croissantking/G3-Personality-Card-USB/Whisper/Whisper Card USB V2.kicad_sch

## KiCad design Whisper/Whisper Card USB V2.kicad_sch (2023-07-12)

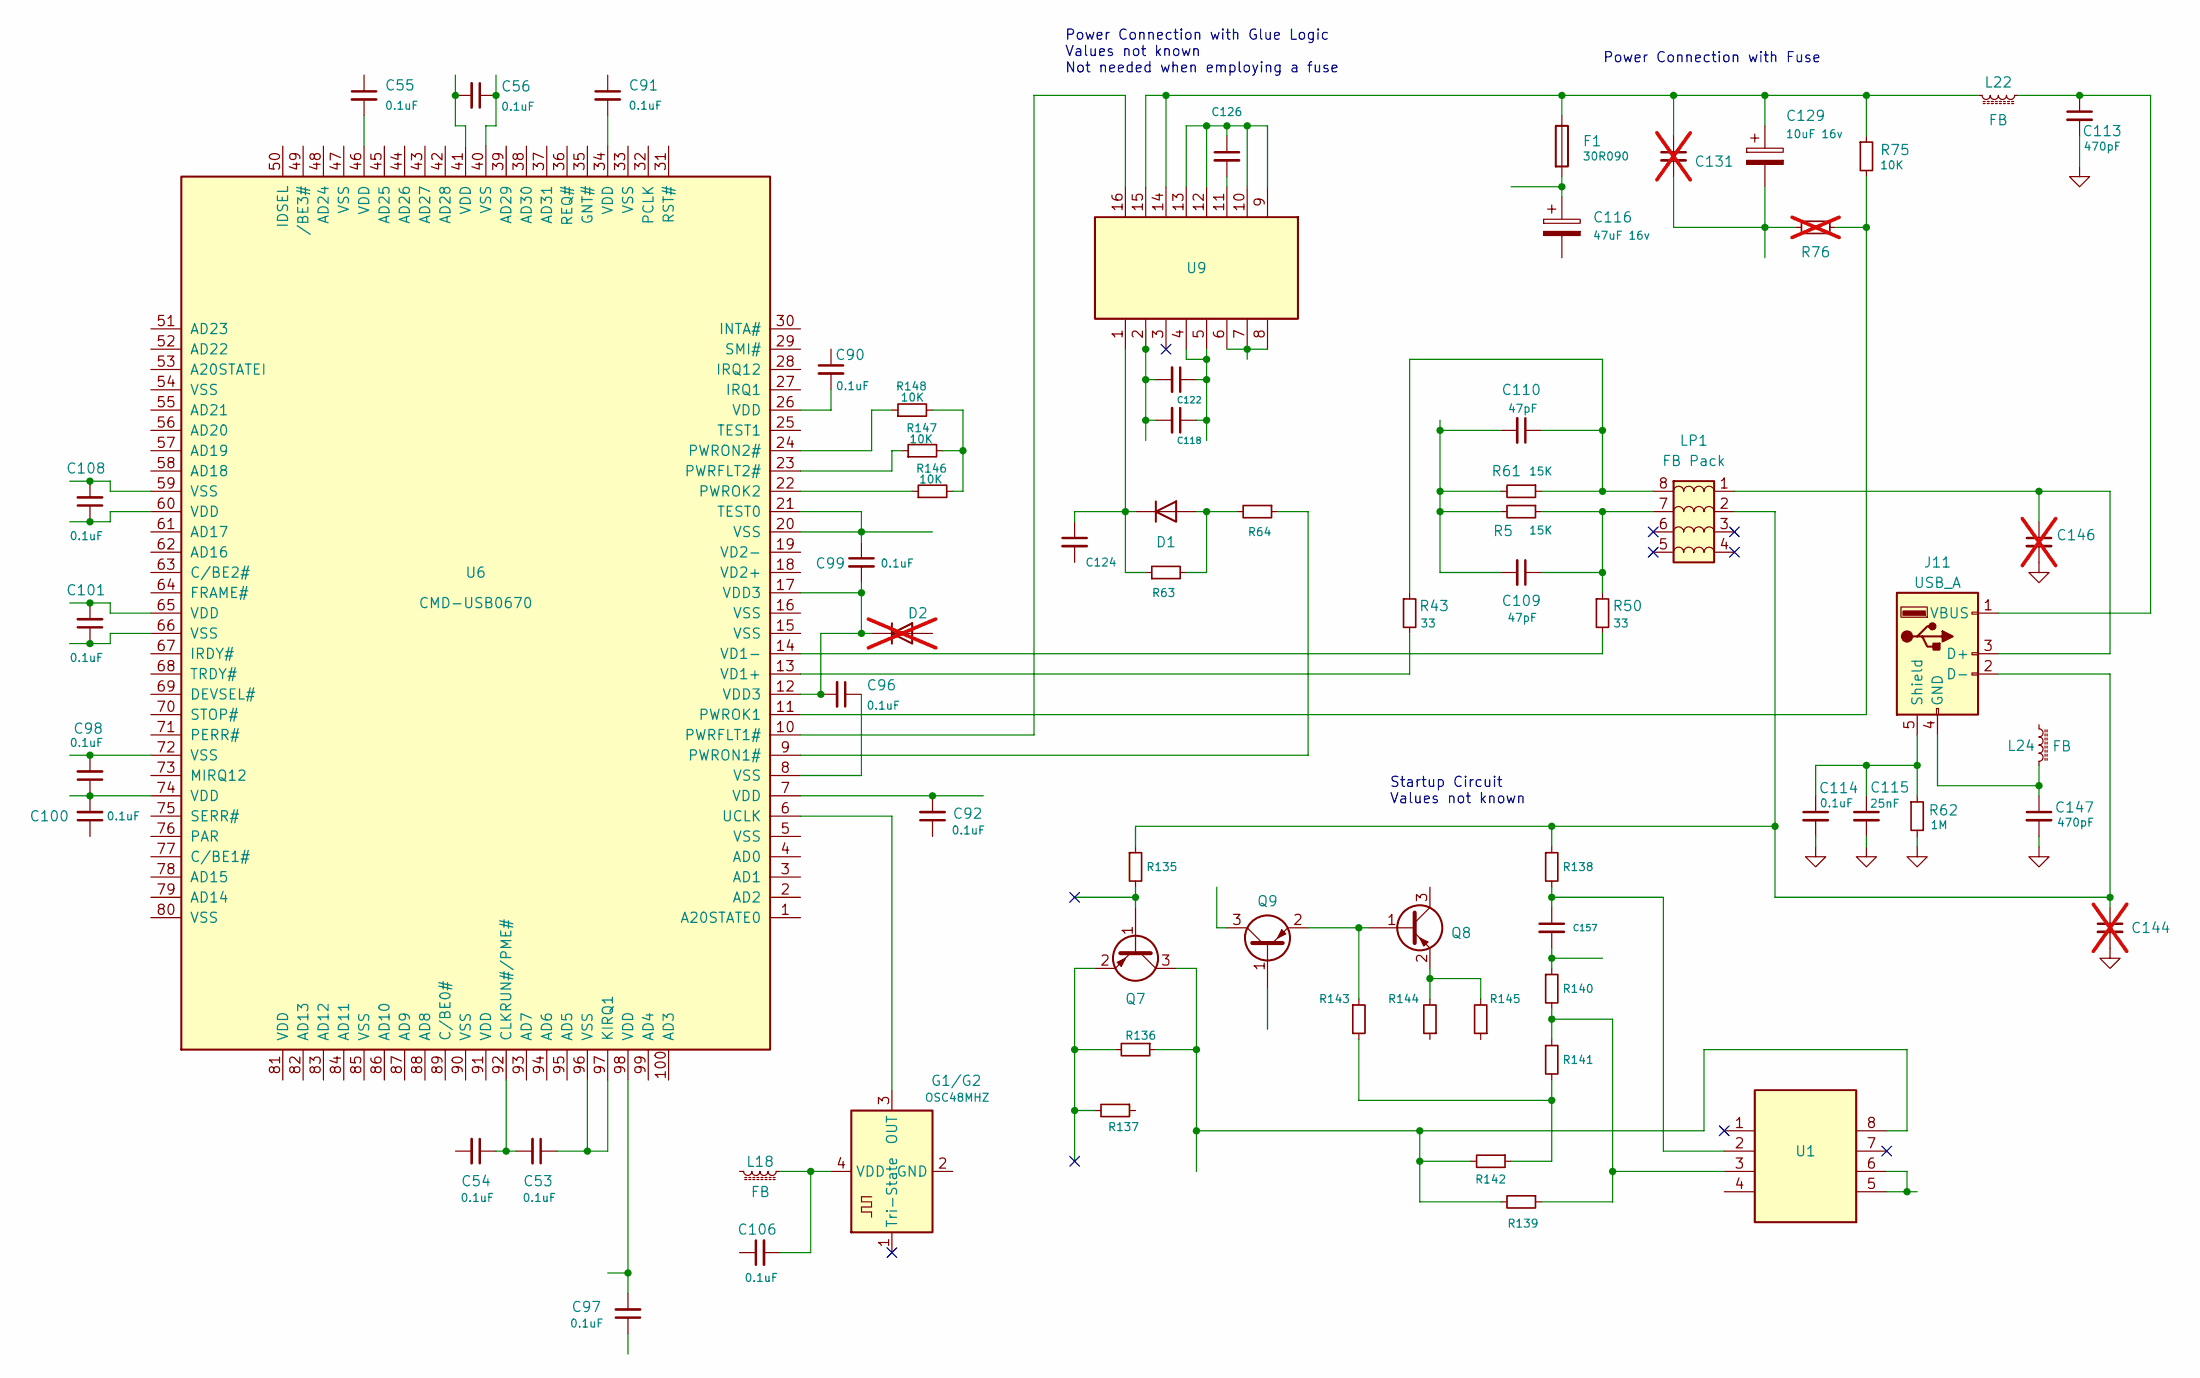
[picture p8: schematic Whisper Card USB V2.kicad_sch]

Parts:
C53, C54, C55, C56, C90, C91, C92, C96, C97, C98, C99, C100, C101, C106, C108, C114: 0.1uF
C109, C110: 47pF
C113, C147: 470pF
C115: 25nF
C116: 47uF 16v
C118, C122, C124, C126, C157: C_Small
C129: 10uF 16v
C131: 1.1nf; not fitted
C144, C146: ???; not fitted
D1: D
D2: D; not fitted
F1: 30R090
G1/G2: OSC48MHZ; Oscillator_SMD_Abracon_ASCO-4Pin_1.6x1.2mm
J11: USB_A
L18, L22, L24: FB
LP1: FB Pack
Q7, Q8, Q9: MMBT3906; SOT-23
R5, R61: 15K
R43, R50: 33
R62: 1M
R63, R64, R135, R136, R137, R138, R139, R140, R141, R142, R143, R144, R145: R_Small
R75, R146, R147, R148: 10K
R76: not fitted
U1, U9: LTC1865-S8; SOIC-8_3.9x4.9mm_P1.27mm
U6: CMD-USB0670; LQFP-100_14x14mm_P0.5mm

Connections:
GND: C113.2, C114.2, C115.2, C144.2, C146.2, C147.2, R62.2
unnamed: C53.1, U6.96 (VSS), U6.97 (KIRQ1)
unnamed: C53.2, C54.1, U6.92 (CLKRUN#/PME#)
unnamed: C55.2, U6.46 (VDD)
unnamed: C56.1, U6.40 (VSS)
unnamed: C56.2, U6.41 (VDD)
unnamed: C90.2, U6.26 (VDD)
unnamed: C91.2, U6.34 (VDD)
unnamed: C92.2, U6.7 (VDD)
unnamed: C96.1, U6.8 (VSS)
unnamed: C96.2, C99.2, D2.1 (K), U6.12 (VDD3), U6.17 (VDD3)
unnamed: C97.2, U6.98 (VDD)
unnamed: C98.2, U6.72 (VSS)
unnamed: C99.1, U6.20 (VSS), U6.21 (TEST0)
unnamed: C98.1, C100.2, U6.74 (VDD)
unnamed: C101.1, U6.66 (VSS)
unnamed: C101.2, U6.65 (VDD)
unnamed: C106.2, G1/G2.4 (VDD), L18.1
unnamed: C108.1, U6.60 (VDD)
unnamed: C108.2, U6.59 (VSS)
unnamed: C109.1, LP1.7, R5.1, R50.1
unnamed: C109.2, C110.2, R5.2, R61.2
unnamed: C110.1, LP1.8, R43.1, R61.1
unnamed: C113.1, J11.1 (VBUS), L22.1
unnamed: C114.1, C115.1, J11.5 (Shield), R62.1
unnamed: C116.1, F1.2
unnamed: C118.1, C122.1, U9.4, U9.5
unnamed: C118.2, C122.2, U9.2
unnamed: C124.1, D1.1 (K), R63.1, U9.1
unnamed: C126.1, U9.9, U9.10, U9.12, U9.13
unnamed: C126.2, U9.11
unnamed: C129.1, C131.1, F1.1, L22.2, R75.1, U9.14, U9.15
unnamed: C129.2, C131.2, R76.2
unnamed: C144.1, J11.2 (D-), LP1.2, R135.1, R138.1
unnamed: C146.1, J11.3 (D+), LP1.1
unnamed: C147.1, J11.4 (GND), L24.2
unnamed: C157.1, R138.2, U1.2
unnamed: C157.2, R140.1
unnamed: D1.2 (A), R63.2, R64.2
unnamed: G1/G2.3 (OUT), U6.6 (UCLK)
unnamed: Q7.1 (B), R135.2
unnamed: Q7.2 (E), R136.2, R137.2
unnamed: Q7.3 (C), R136.1, R139.2, R142.2, U1.8
unnamed: Q8.1 (B), Q9.2 (E), R143.1
unnamed: Q8.2 (E), R144.2, R145.2
unnamed: R43.2, U6.13 (VD1+)
unnamed: R50.2, U6.14 (VD1-)
unnamed: R64.1, U6.9 (PWRON1#)
unnamed: R75.2, R76.1, U6.11 (PWROK1)
unnamed: R139.1, R140.2, R141.1, U1.3
unnamed: R141.2, R142.1, R143.2
unnamed: R146.1, U6.22 (PWROK2)
unnamed: R146.2, R147.2, R148.2
unnamed: R147.1, U6.23 (PWRFLT2#)
unnamed: R148.1, U6.24 (PWRON2#)
unnamed: U1.5, U1.6
unnamed: U6.10 (PWRFLT1#), U9.16
unnamed: U9.6, U9.7, U9.8

Notes on the sheet:
Startup Circuit Values not known
Power Connection with Glue Logic Values not known Not needed when employing a fuse
Power Connection with Fuse
