croissantking/G3-Personality-Card-USB/Whisper/Whisper USB V5.kicad_sch

## KiCad design Whisper/Whisper USB V5.kicad_sch (2025-03-09)

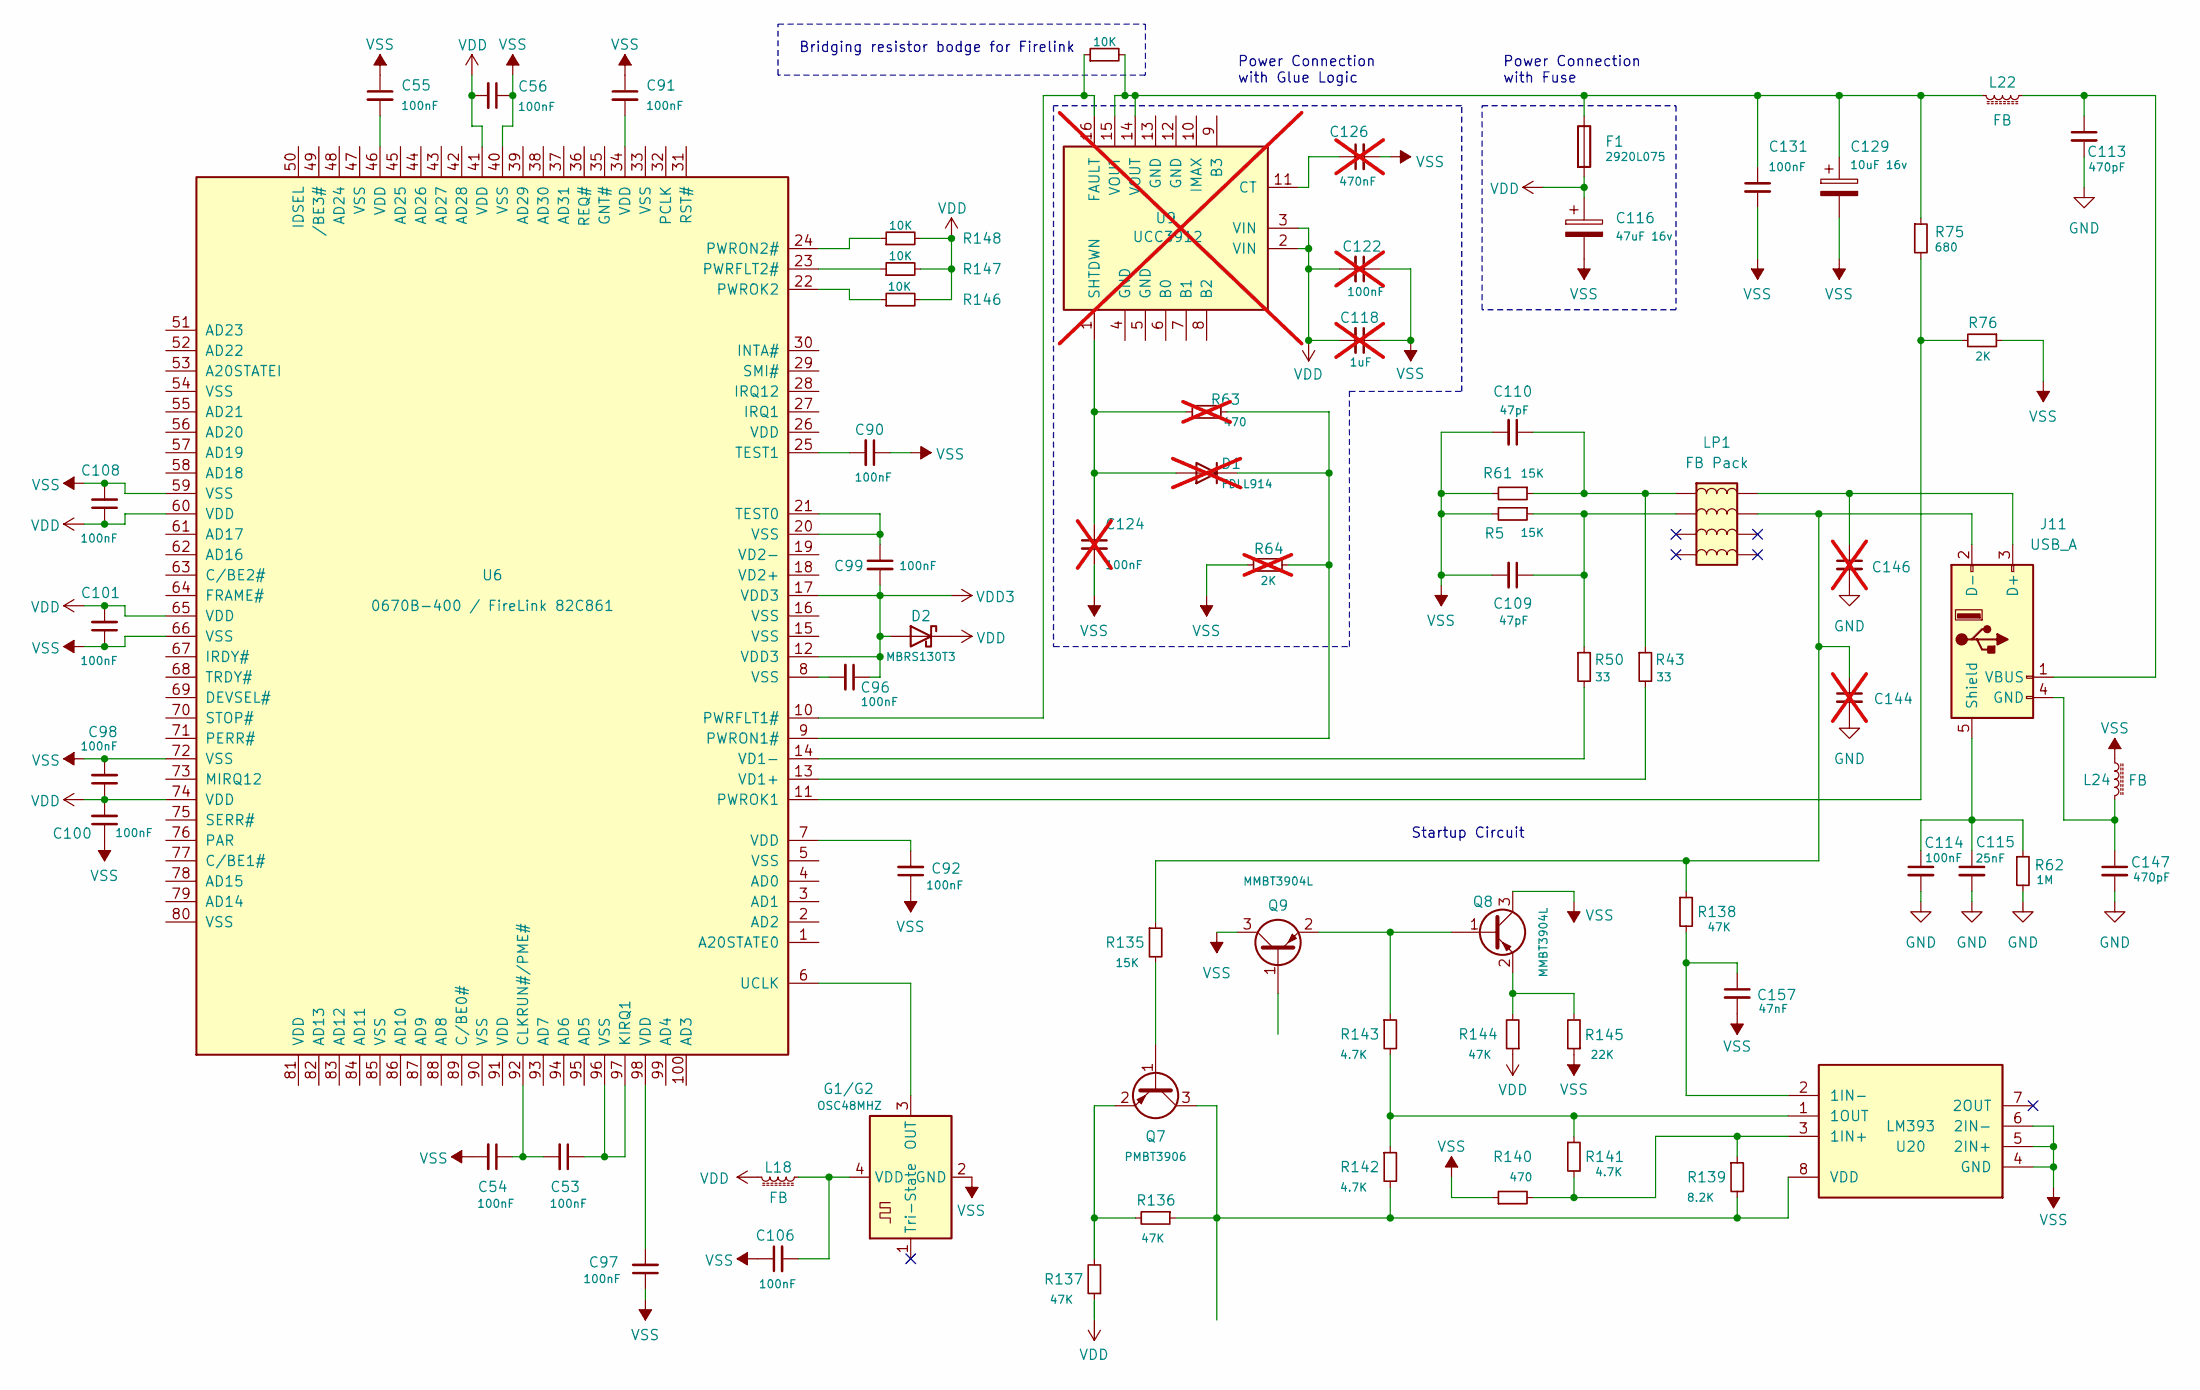
[picture p9: schematic Whisper USB V5.kicad_sch]

Parts:
C53, C54, C55, C56, C90, C91, C92, C96, C97, C98, C99, C100, C101, C106, C108, C114, C131: 100nF
C109, C110: 47pF
C113, C147: 470pF
C115: 25nF
C116: 47uF 16v
C118: 1uF; not fitted
C122, C124: 100nF; not fitted
C126: 470nF; not fitted
C129: 10uF 16v
C144, C146: ???; not fitted
C157: 47nF
D1: FDLL914; not fitted
D2: MBRS130T3
F1: 2920L075
G1/G2: OSC48MHZ; Oscillator_SMD_Abracon_ASCO-4Pin_1.6x1.2mm
J11: USB_A
L18, L22, L24: FB
LP1: FB Pack
Q7: PMBT3906; SOT-23
Q8, Q9: MMBT3904L; SOT-23
R1, R146, R147, R148: 10K
R5, R61, R135: 15K
R43, R50: 33
R62: 1M
R63: 470; not fitted
R64: 2K; not fitted
R75: 680
R76: 2K
R136, R137, R138, R144: 47K
R139: 8.2K
R140: 470
R141, R142, R143: 4.7K
R145: 22K
U6: 0670B-400 / FireLink 82C861; LQFP-100_14x14mm_P0.5mm
U9: UCC3912; SOIC-8_3.9x4.9mm_P1.27mm; not fitted
U20: LM393; SOIC-8_3.9x4.9mm_P1.27mm

Connections:
GND: C113.2, C114.2, C115.2, C144.2, C146.2, C147.2, R62.2
unnamed: C53.1, U6.96 (VSS), U6.97 (KIRQ1)
unnamed: C53.2, C54.1, U6.92 (CLKRUN#/PME#)
unnamed: C55.2, U6.46 (VDD)
unnamed: C90.2, U6.25 (TEST1)
unnamed: C91.2, U6.34 (VDD)
unnamed: C92.2, U6.7 (VDD)
unnamed: C96.2, U6.8 (VSS)
unnamed: C97.2, U6.98 (VDD)
unnamed: C99.1, U6.20 (VSS), U6.21 (TEST0)
unnamed: C106.2, G1/G2.4 (VDD), L18.1
unnamed: C109.1, LP1.7, R5.1, R50.1
unnamed: C110.1, LP1.8, R43.1, R61.1
unnamed: C113.1, J11.1 (VBUS), L22.1
unnamed: C114.1, C115.1, J11.5 (Shield), R62.1
unnamed: C124.1, D1.2 (A), R63.1, U9.1 (SHTDWN)
unnamed: C126.1, U9.11 (CT)
unnamed: C129.1, C131.1, F1.1, L22.2, R1.2, R75.1, U9.14 (VOUT), U9.15 (VOUT)
unnamed: C144.1, J11.2 (D-), LP1.2, R135.1, R138.1
unnamed: C146.1, J11.3 (D+), LP1.1
unnamed: C147.1, J11.4 (GND), L24.2
unnamed: C157.1, R138.2, U20.2 (1IN-)
unnamed: D1.1 (K), R63.2, R64.1, U6.9 (PWRON1#)
unnamed: G1/G2.3 (OUT), U6.6 (UCLK)
unnamed: Q7.1 (B), R135.2
unnamed: Q7.2 (E), R136.2, R137.2
unnamed: Q7.3 (C), R136.1, R139.2, R142.2, U20.8 (VDD)
unnamed: Q8.1 (B), Q9.2 (E), R143.1
unnamed: Q8.2 (E), R144.2, R145.2
unnamed: R1.1, U6.10 (PWRFLT1#), U9.16 (FAULT)
unnamed: R43.2, U6.13 (VD1+)
unnamed: R50.2, U6.14 (VD1-)
unnamed: R75.2, R76.2, U6.11 (PWROK1)
unnamed: R139.1, R140.2, R141.2, U20.3 (1IN+)
unnamed: R141.1, R142.1, R143.2, U20.1 (1OUT)
unnamed: R146.1, U6.22 (PWROK2)
unnamed: R147.1, U6.23 (PWRFLT2#)
unnamed: R148.1, U6.24 (PWRON2#)
VDD: C56.2, C98.1, C100.2, C101.2, C108.1, C116.1, C118.2, C122.2, D2.1 (K), F1.2, L18.2, R137.1, R144.1, R146.2, R147.2, R148.2, U6.41 (VDD), U6.60 (VDD), U6.65 (VDD), U6.74 (VDD), U9.2 (VIN), U9.3 (VIN)
VDD3: C96.1, C99.2, D2.2 (A), U6.12 (VDD3), U6.17 (VDD3)
VSS: C54.2, C55.1, C56.1, C90.1, C91.1, C92.1, C97.1, C98.2, C100.1, C101.1, C106.1, C108.2, C109.2, C110.2, C116.2, C118.1, C122.1, C124.2, C126.2, C129.2, C131.2, C157.2, G1/G2.2 (GND), L24.1, Q8.3 (C), Q9.3 (C), R5.2, R61.2, R64.2, R76.1, R140.1, R145.1, U6.40 (VSS), U6.59 (VSS), U6.66 (VSS), U6.72 (VSS), U20.4 (GND), U20.5 (2IN+), U20.6 (2IN-)

Notes on the sheet:
Startup Circuit
Power Connection with Glue Logic
Power Connection with Fuse
Bridging resistor bodge for Firelink
