croissantking/G3-Personality-Card-USB/Wings/Wings USB V3.kicad_sch

## KiCad design Wings/Wings USB V3.kicad_sch (2025-03-09)

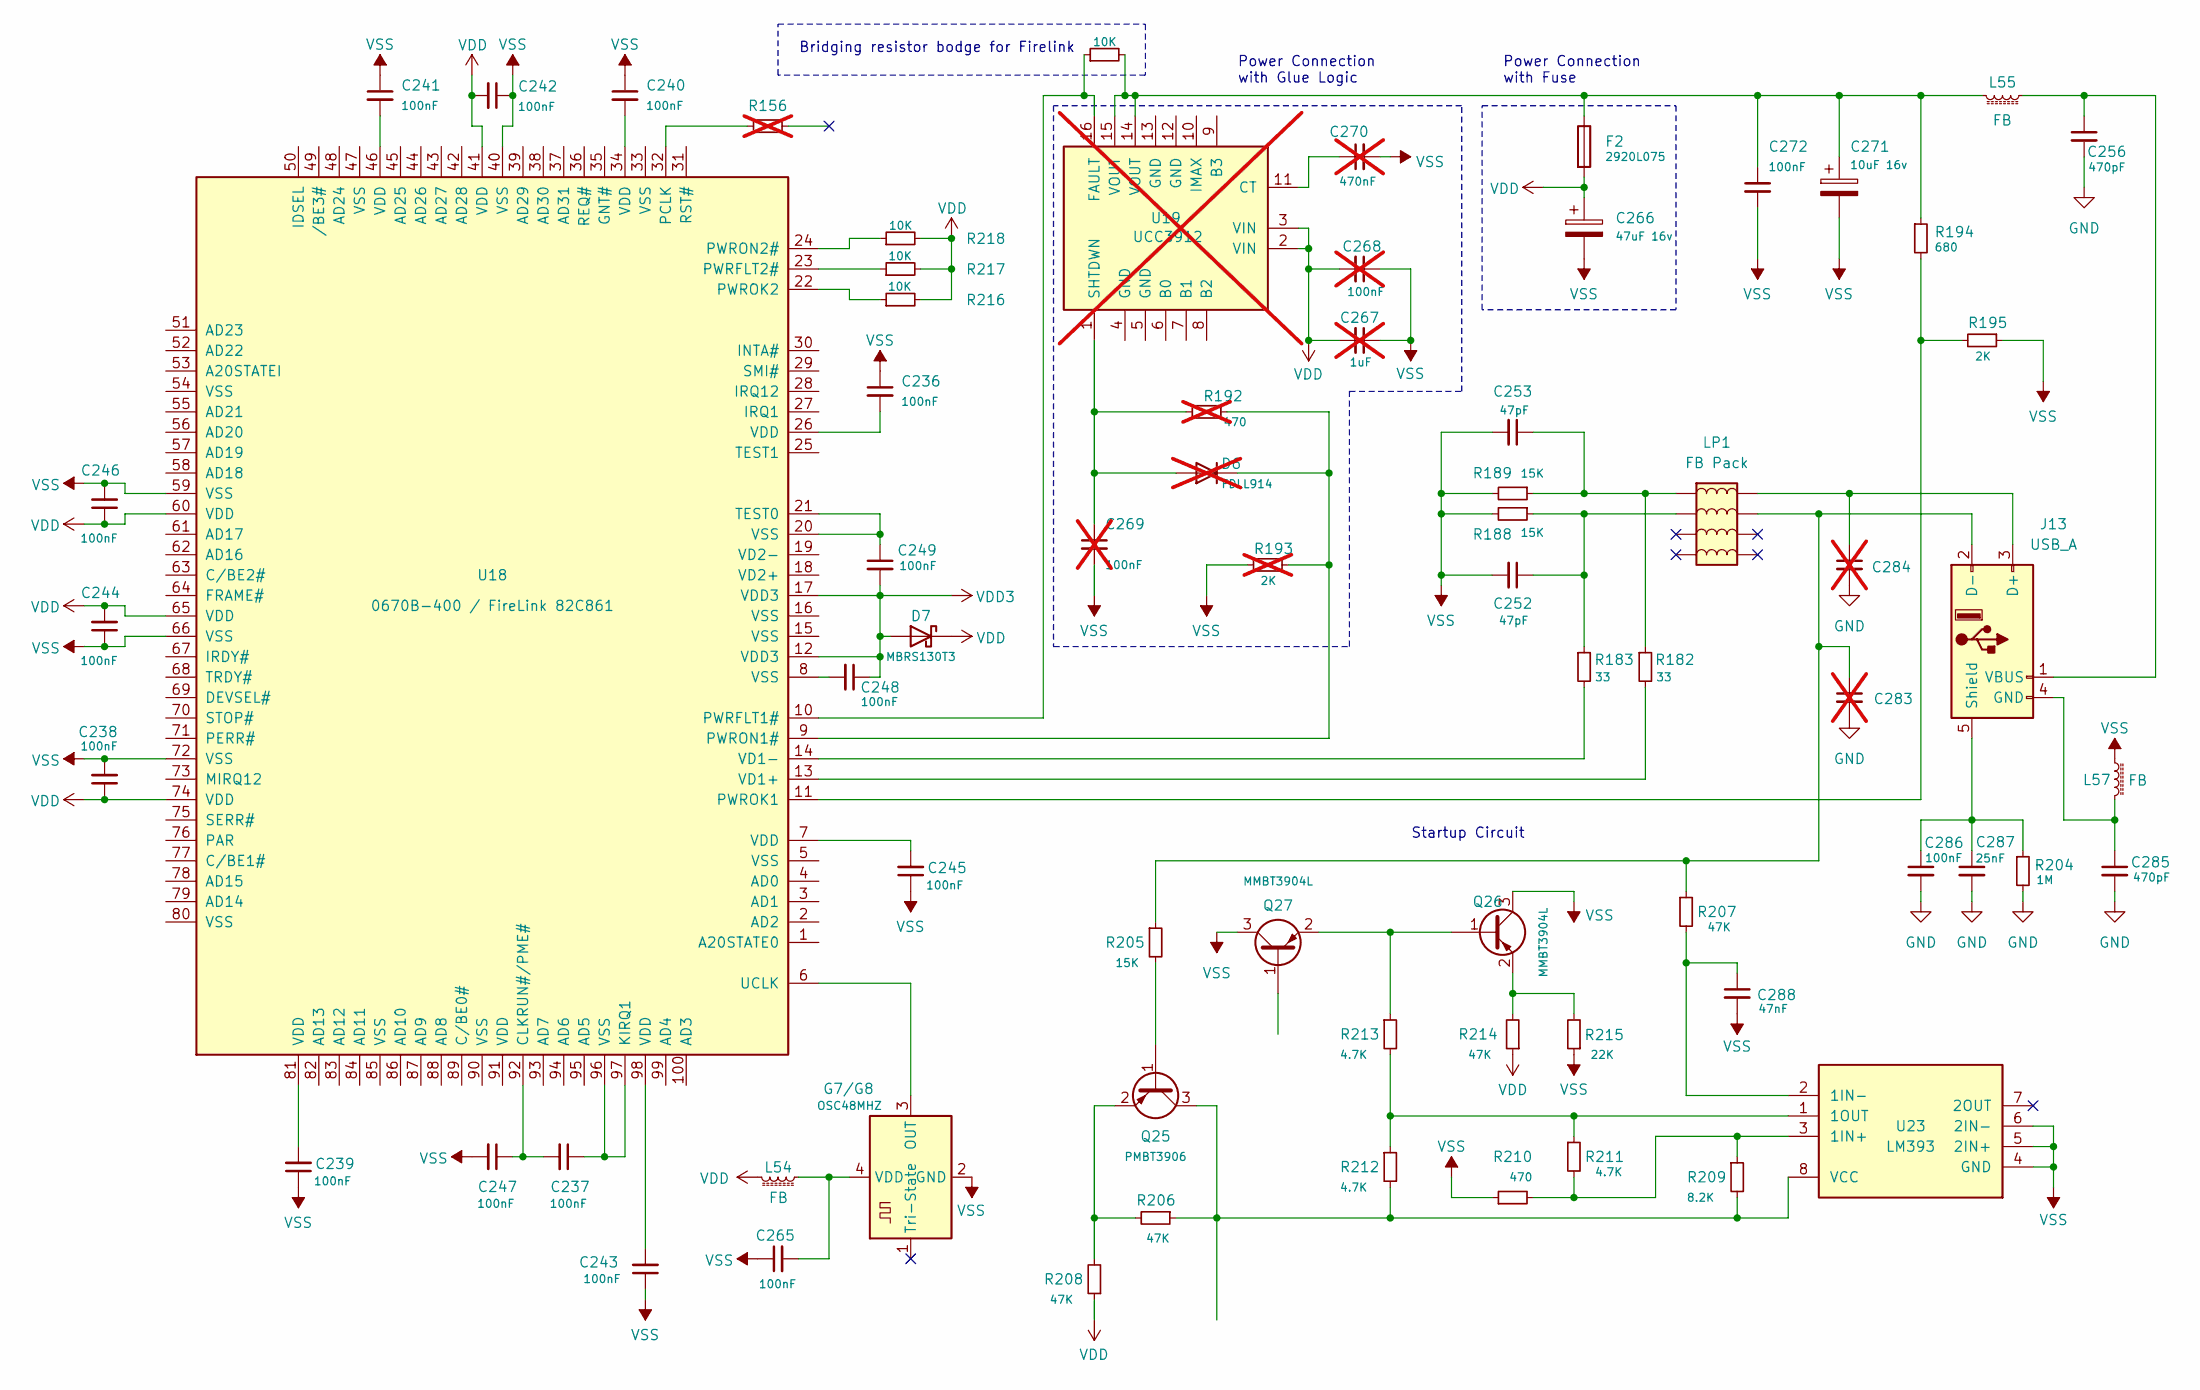
[picture p10: schematic Wings USB V3.kicad_sch]

Parts:
C236, C237, C238, C239, C240, C241, C242, C243, C244, C245, C246, C247, C248, C249, C265, C272, C286: 100nF
C252, C253: 47pF
C256, C285: 470pF
C266: 47uF 16v
C267: 1uF; not fitted
C268, C269: 100nF; not fitted
C270: 470nF; not fitted
C271: 10uF 16v
C283, C284: ???; not fitted
C287: 25nF
C288: 47nF
D6: FDLL914; not fitted
D7: MBRS130T3
F2: 2920L075
G7/G8: OSC48MHZ; Oscillator_SMD_Abracon_ASCO-4Pin_1.6x1.2mm
J13: USB_A
L54, L55, L57: FB
LP1: FB Pack
Q25: PMBT3906; SOT-23
Q26, Q27: MMBT3904L; SOT-23
R1, R216, R217, R218: 10K
R156, R192: 470; not fitted
R182, R183: 33
R188, R189, R205: 15K
R193: 2K; not fitted
R194: 680
R195: 2K
R204: 1M
R206, R207, R208, R214: 47K
R209: 8.2K
R210: 470
R211, R212, R213: 4.7K
R215: 22K
U18: 0670B-400 / FireLink 82C861; LQFP-100_14x14mm_P0.5mm
U19: UCC3912; SOIC-8_3.9x4.9mm_P1.27mm; not fitted
U23: LM393; SOIC-8_3.9x4.9mm_P1.27mm

Connections:
GND: C256.2, C283.2, C284.2, C285.2, C286.2, C287.2, R204.2
unnamed: C236.2, U18.26 (VDD)
unnamed: C237.1, U18.96 (VSS), U18.97 (KIRQ1)
unnamed: C237.2, C247.1, U18.92 (CLKRUN#/PME#)
unnamed: C239.2, U18.81 (VDD)
unnamed: C240.2, U18.34 (VDD)
unnamed: C241.2, U18.46 (VDD)
unnamed: C243.2, U18.98 (VDD)
unnamed: C245.2, U18.7 (VDD)
unnamed: C248.2, U18.8 (VSS)
unnamed: C249.1, U18.20 (VSS), U18.21 (TEST0)
unnamed: C252.1, LP1.7, R183.1, R188.1
unnamed: C253.1, LP1.8, R182.1, R189.1
unnamed: C256.1, J13.1 (VBUS), L55.1
unnamed: C265.2, G7/G8.4 (VDD), L54.1
unnamed: C269.1, D6.2 (A), R192.1, U19.1 (SHTDWN)
unnamed: C270.1, U19.11 (CT)
unnamed: C271.1, C272.1, F2.1, L55.2, R1.2, R194.1, U19.14 (VOUT), U19.15 (VOUT)
unnamed: C283.1, J13.2 (D-), LP1.2, R205.1, R207.1
unnamed: C284.1, J13.3 (D+), LP1.1
unnamed: C285.1, J13.4 (GND), L57.2
unnamed: C286.1, C287.1, J13.5 (Shield), R204.1
unnamed: C288.1, R207.2, U23.2 (1IN-)
unnamed: D6.1 (K), R192.2, R193.1, U18.9 (PWRON1#)
unnamed: G7/G8.3 (OUT), U18.6 (UCLK)
unnamed: Q25.1 (B), R205.2
unnamed: Q25.2 (E), R206.2, R208.2
unnamed: Q25.3 (C), R206.1, R209.2, R212.2, U23.8 (VCC)
unnamed: Q26.1 (B), Q27.2 (E), R213.1
unnamed: Q26.2 (E), R214.2, R215.2
unnamed: R1.1, U18.10 (PWRFLT1#), U19.16 (FAULT)
unnamed: R156.1, U18.32 (PCLK)
unnamed: R182.2, U18.13 (VD1+)
unnamed: R183.2, U18.14 (VD1-)
unnamed: R194.2, R195.2, U18.11 (PWROK1)
unnamed: R209.1, R210.2, R211.2, U23.3 (1IN+)
unnamed: R211.1, R212.1, R213.2, U23.1 (1OUT)
unnamed: R216.1, U18.22 (PWROK2)
unnamed: R217.1, U18.23 (PWRFLT2#)
unnamed: R218.1, U18.24 (PWRON2#)
VDD: C238.1, C242.2, C244.2, C246.1, C266.1, C267.2, C268.2, D7.1 (K), F2.2, L54.2, R208.1, R214.1, R216.2, R217.2, R218.2, U18.41 (VDD), U18.60 (VDD), U18.65 (VDD), U18.74 (VDD), U19.2 (VIN), U19.3 (VIN)
VDD3: C248.1, C249.2, D7.2 (A), U18.12 (VDD3), U18.17 (VDD3)
VSS: C236.1, C238.2, C239.1, C240.1, C241.1, C242.1, C243.1, C244.1, C245.1, C246.2, C247.2, C252.2, C253.2, C265.1, C266.2, C267.1, C268.1, C269.2, C270.2, C271.2, C272.2, C288.2, G7/G8.2 (GND), L57.1, Q26.3 (C), Q27.3 (C), R188.2, R189.2, R193.2, R195.1, R210.1, R215.1, U18.40 (VSS), U18.59 (VSS), U18.66 (VSS), U18.72 (VSS), U23.4 (GND), U23.5 (2IN+), U23.6 (2IN-)

Notes on the sheet:
Bridging resistor bodge for Firelink
Startup Circuit
Power Connection with Glue Logic
Power Connection with Fuse
